FEEprojects/pi-seb/v1-0/parts-placement.pdf

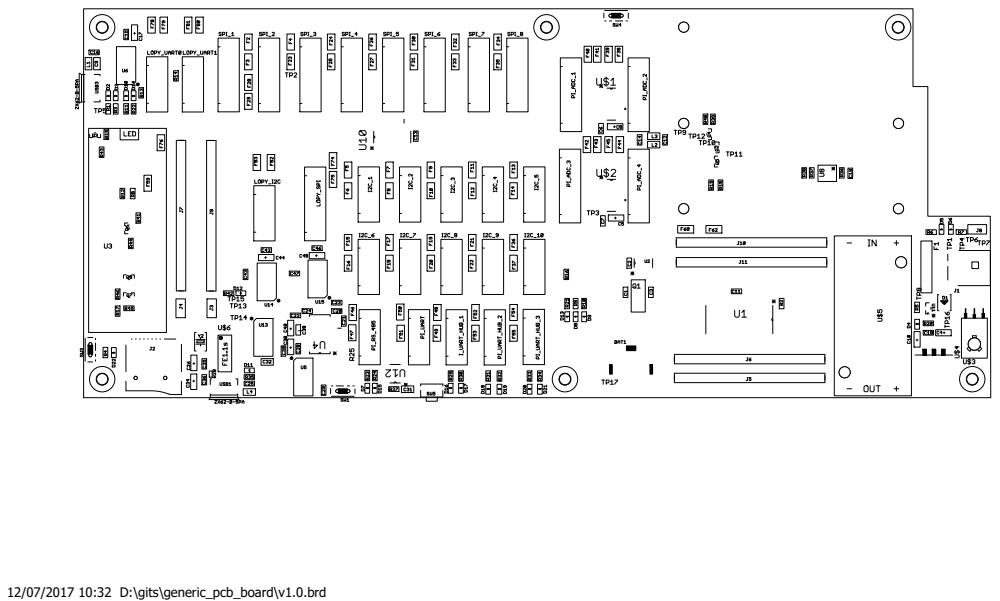
[picture p5: page 1]
12/07/2017 10:32 D:\gits\generic_pcb_board\v1.0.brd
